DL2DW/ZX1541-Interface_in_THT/files_found_on_the_internet/Pictures/0001a.jpg

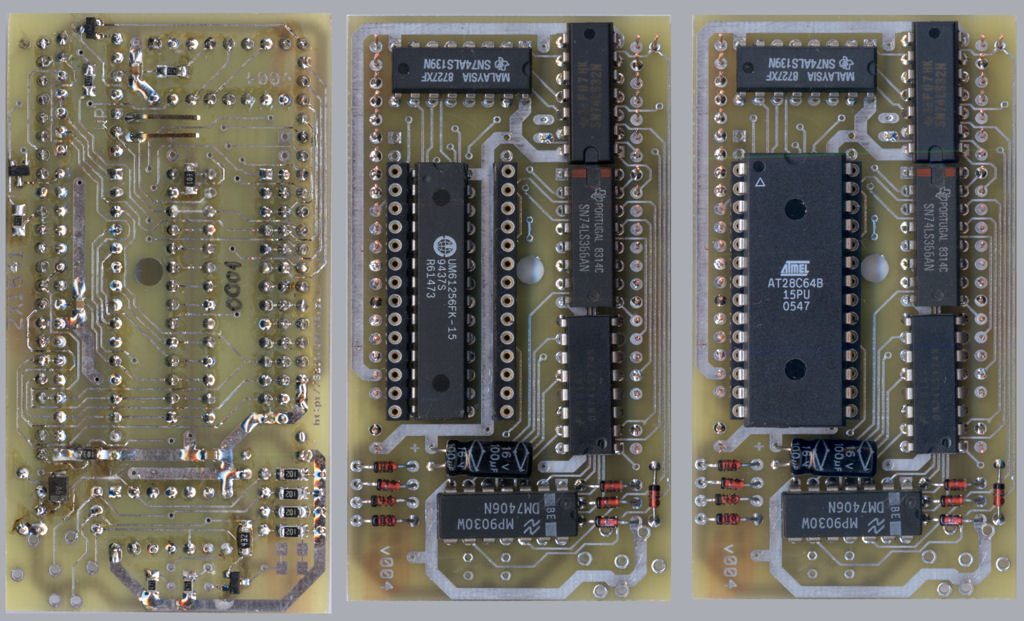
files_found_on_the_internet/Pictures/0001a.jpg
