DL2DW/ZX1541-Interface_in_THT/files_found_on_the_internet/Pictures/0003b.jpg

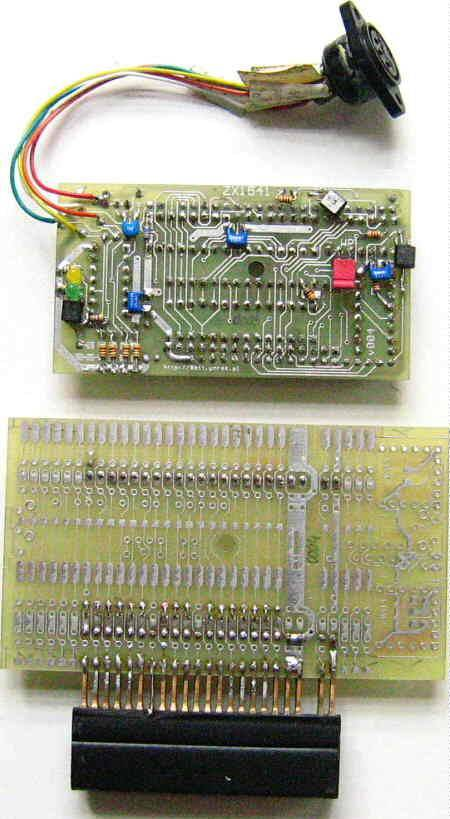
files_found_on_the_internet/Pictures/0003b.jpg
