DL2DW/ZX1541-Interface_in_THT/files_found_on_the_internet/Pictures/disk2.jpg

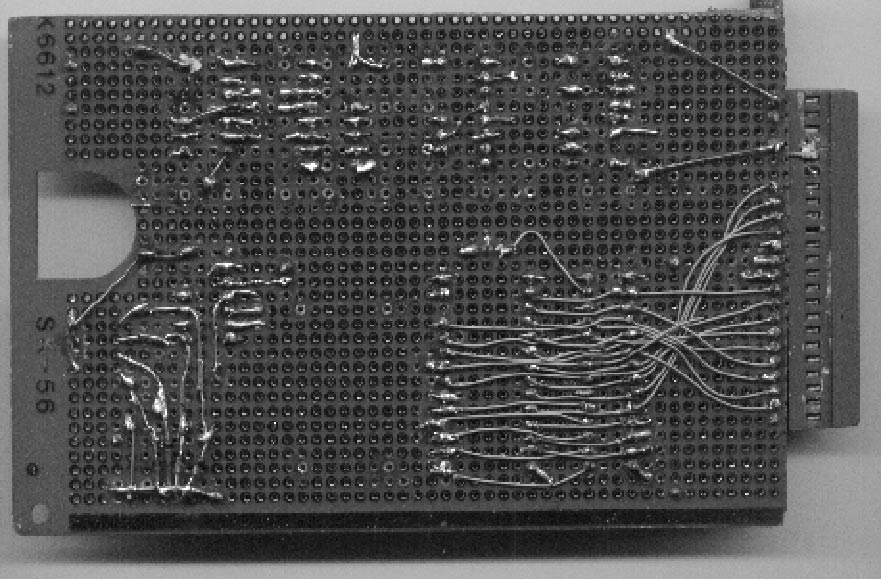
files_found_on_the_internet/Pictures/disk2.jpg
