DL2DW/ZX1541-Interface_in_THT/files_found_on_the_internet/Pictures/ZX1541 SMD PCB New.png

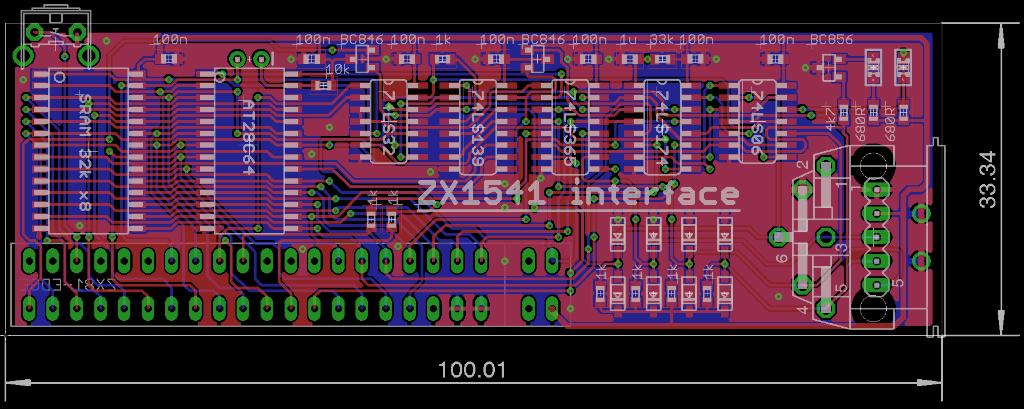
files_found_on_the_internet/Pictures/ZX1541 SMD PCB New.png
